ConDarth/MidiEVS/Documentation/EVIPCBLayout/EVIValvePCB.dxf

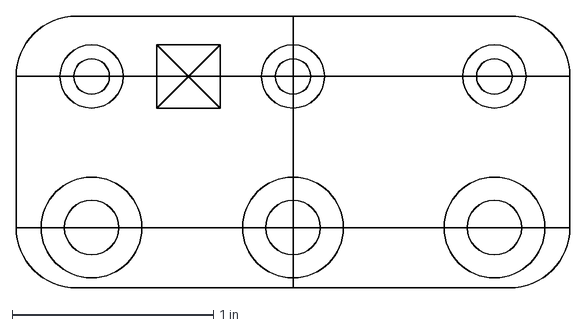
[picture p17: CAD file, 2022-07-06]
Documentation/EVIPCBLayout/EVIValvePCB.dxf
2.75 x 1.35 in
