ConDarth/MidiEVS/EVImk1/3d Files/MouthpieceFront.obj

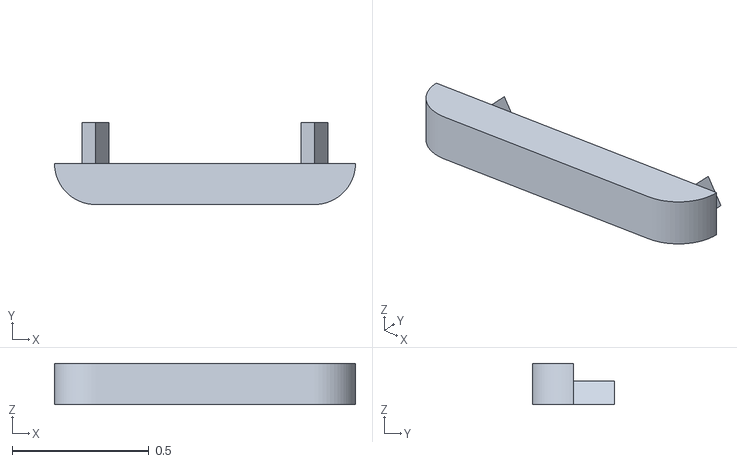
[picture p18: CAD file, 2019-05-07]
EVImk1/3d Files/MouthpieceFront.obj
1.10 x 0.3 x 0.15
