ConDarth/MidiEVS/EVImk3/EVImk3Cannister3.stl

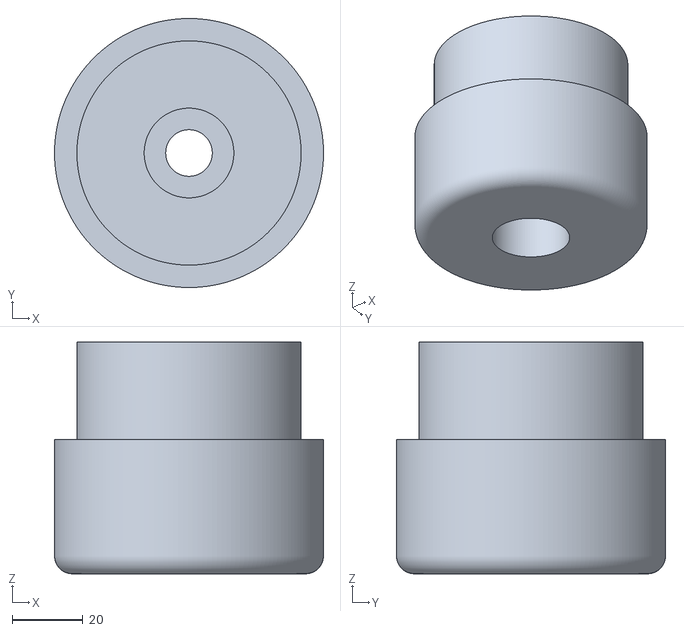
[picture p19: CAD file, 2022-07-06]
EVImk3/EVImk3Cannister3.stl
76.2 x 76.2 x 65.6
