ConDarth/MidiEVS/EVImk4/2D Files/EVImk4LidBottom.dxf

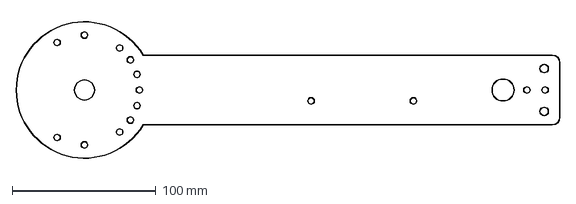
[picture p20: CAD file, 2023-05-10]
EVImk4/2D Files/EVImk4LidBottom.dxf
377.6 x 102.7 mm
