ConDarth/MidiEVS/EVImk4/3D Files/EVImk4Cannister2.stl

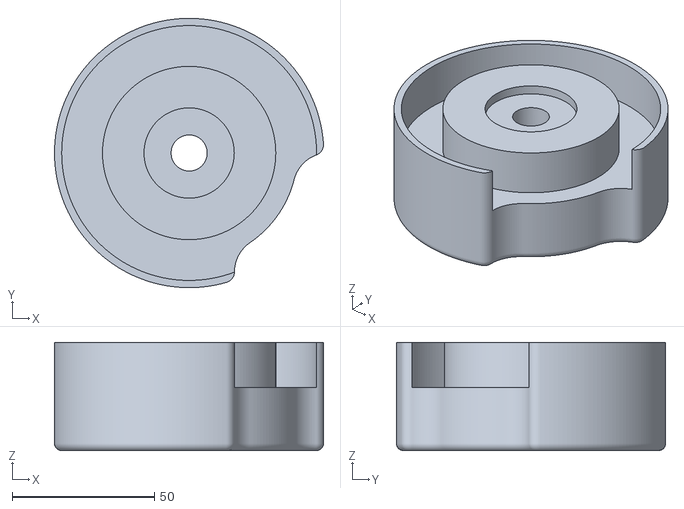
[picture p21: CAD file, 2023-05-10]
EVImk4/3D Files/EVImk4Cannister2.stl
94.6 x 94.7 x 38.1
