ConDarth/MidiEVS/Documentation/EVI3dCAD/Body3.2.stl

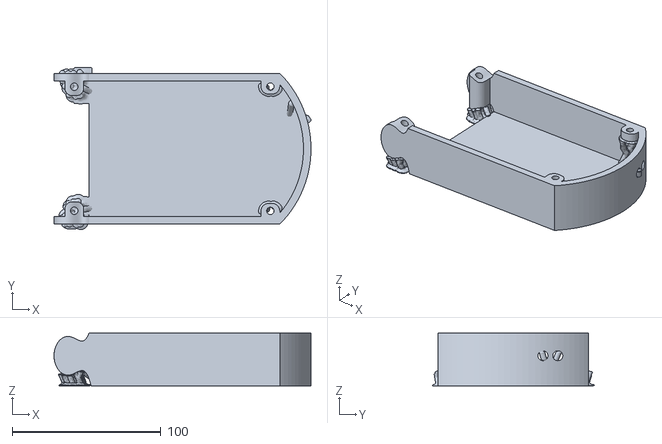
[picture p22: CAD file, 2021-01-06]
Documentation/EVI3dCAD/Body3.2.stl
173.0 x 109.2 x 35.7
