ConDarth/MidiEVS/EVImk1/3d Files/BasicCannsiter.obj

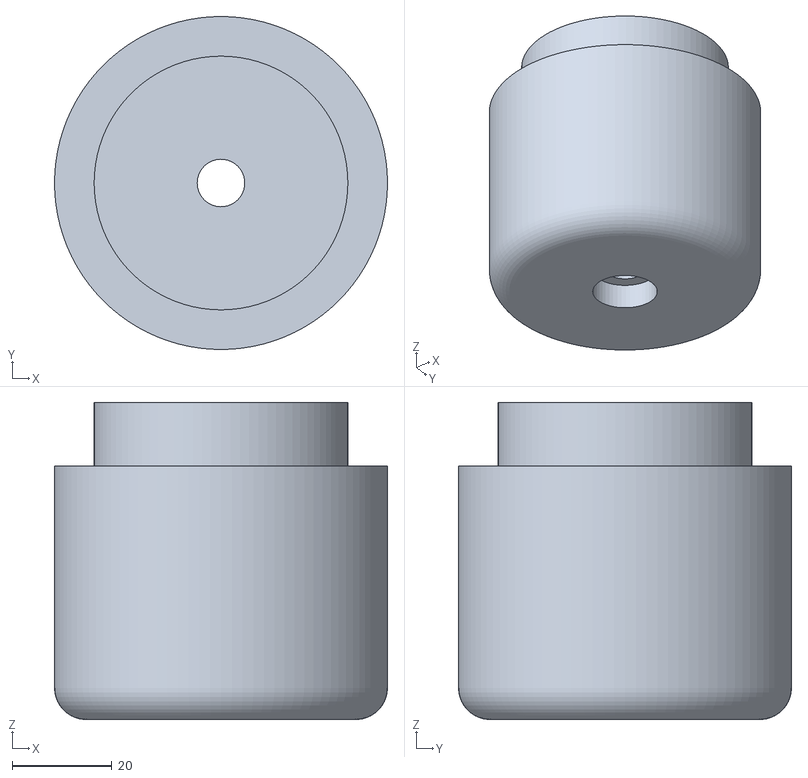
[picture p23: CAD file, 2019-05-07]
EVImk1/3d Files/BasicCannsiter.obj
66.7 x 66.7 x 63.5
