ConDarth/MidiEVS/EVImk3/EVImk3Mouthpeice.stl

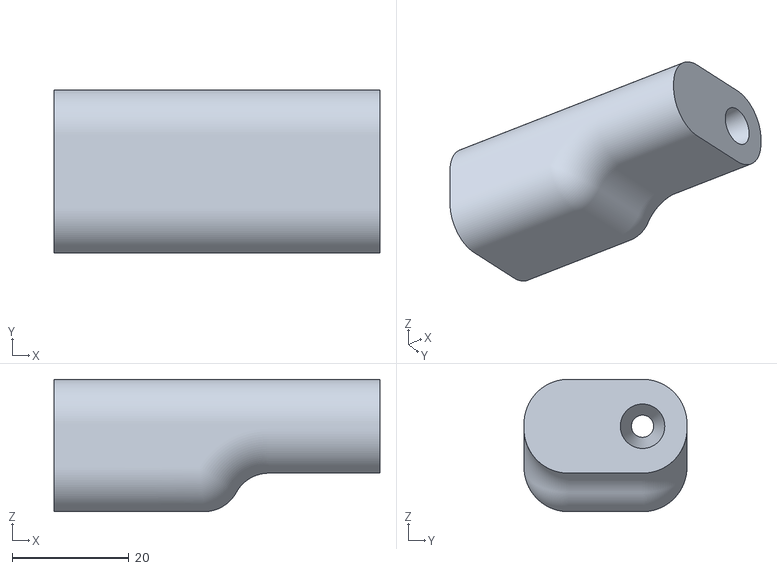
[picture p24: CAD file, 2022-07-06]
EVImk3/EVImk3Mouthpeice.stl
55.9 x 27.9 x 22.7
