ConDarth/MidiEVS/EVImk4/2D Files/EVImk4LidTop.dxf

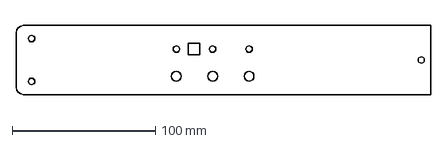
[picture p25: CAD file, 2023-05-10]
EVImk4/2D Files/EVImk4LidTop.dxf
289.4 x 48.3 mm
