ConDarth/MidiEVS/EVImk4/3D Files/EVImk4BodyFront4.stl

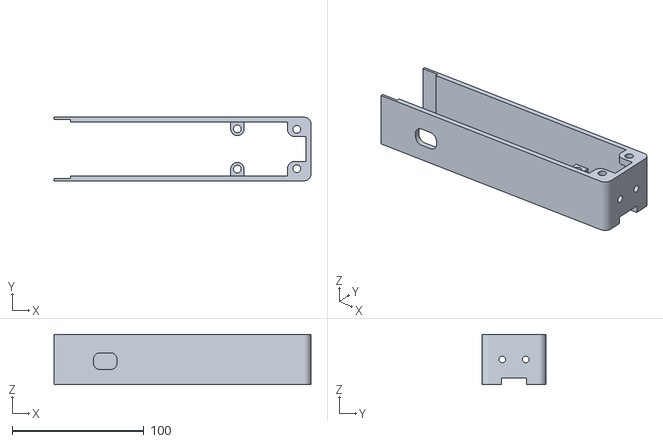
[picture p26: CAD file, 2023-05-10]
EVImk4/3D Files/EVImk4BodyFront4.stl
195.0 x 48.3 x 38.1
