ConDarth/MidiEVS/Documentation/EVI3dCAD/Mouthpeice1.0.stl

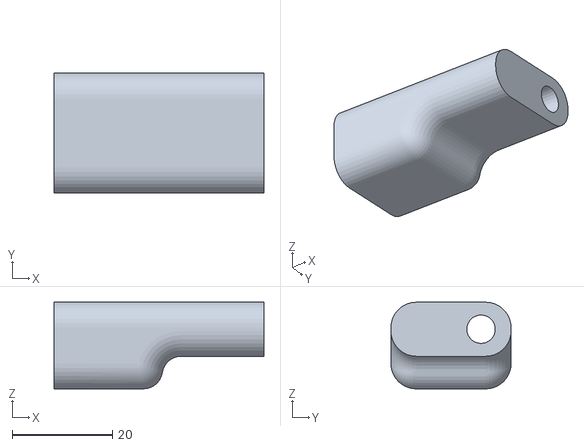
[picture p27: CAD file, 2021-01-06]
Documentation/EVI3dCAD/Mouthpeice1.0.stl
41.9 x 24.0 x 17.3
