ConDarth/MidiEVS/EVImk1/3d Files/MouthpieceTop.obj

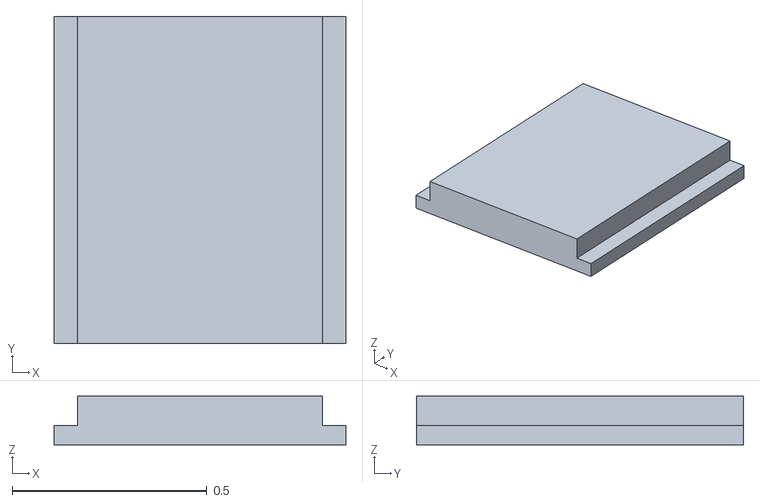
[picture p28: CAD file, 2019-05-07]
EVImk1/3d Files/MouthpieceTop.obj
0.75 x 0.84 x 0.125
