ConDarth/MidiEVS/EVImk3/EVImk3Cannister.stl

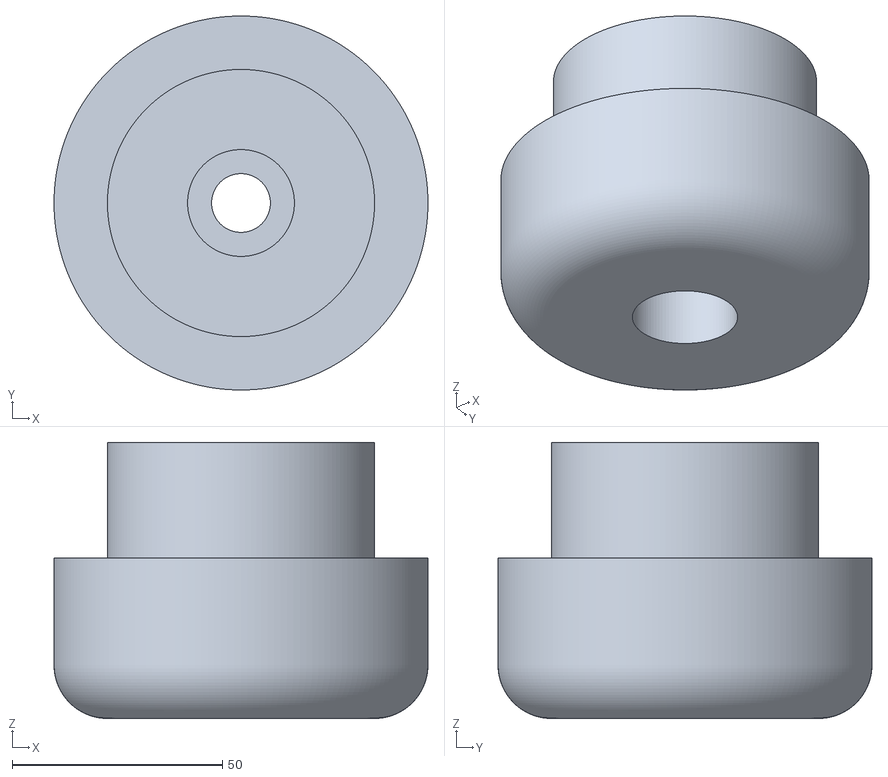
[picture p29: CAD file, 2022-07-06]
EVImk3/EVImk3Cannister.stl
88.9 x 88.9 x 65.6
