ConDarth/MidiEVS/EVImk4/3D Files/EVImk4LidTop.stl

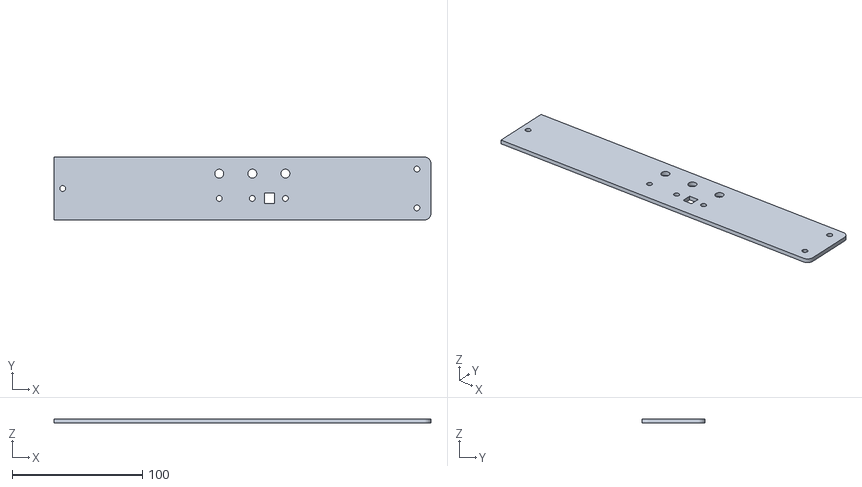
[picture p30: CAD file, 2023-05-10]
EVImk4/3D Files/EVImk4LidTop.stl
289.4 x 48.3 x 3.18
