ConDarth/MidiEVS/Documentation/EVI3dCAD/Body4.1.stl

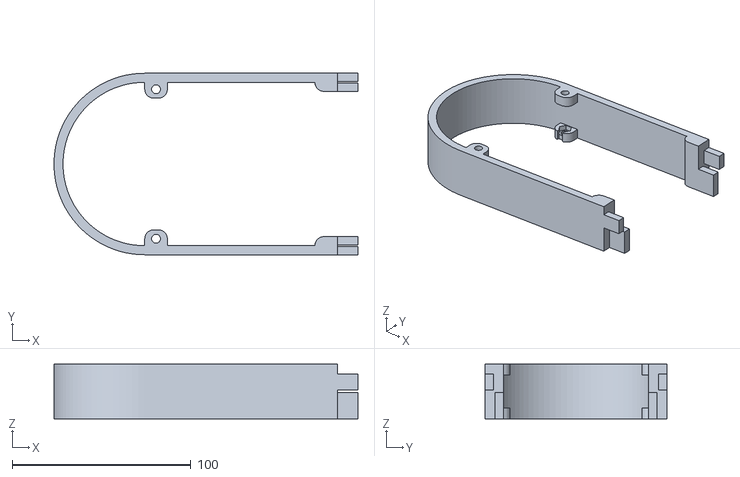
[picture p31: CAD file, 2021-01-06]
Documentation/EVI3dCAD/Body4.1.stl
170.1 x 101.6 x 30.6
