ConDarth/MidiEVS/EVImk3/EVImk3BackPlate.stl

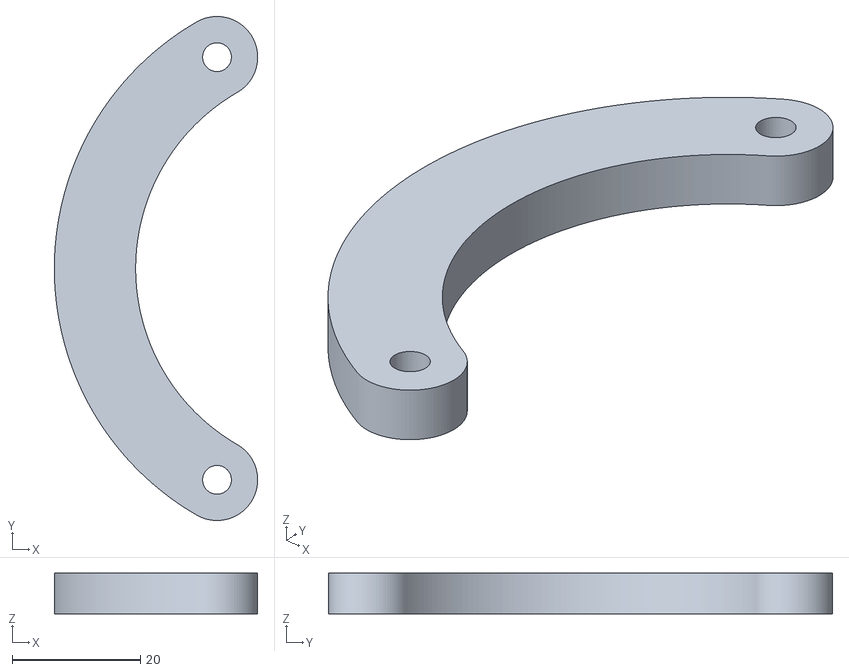
[picture p32: CAD file, 2022-07-06]
EVImk3/EVImk3BackPlate.stl
31.7 x 78.7 x 6.35
