ConDarth/MidiEVS/Documentation/EVI3dCAD/Body2.2.stl

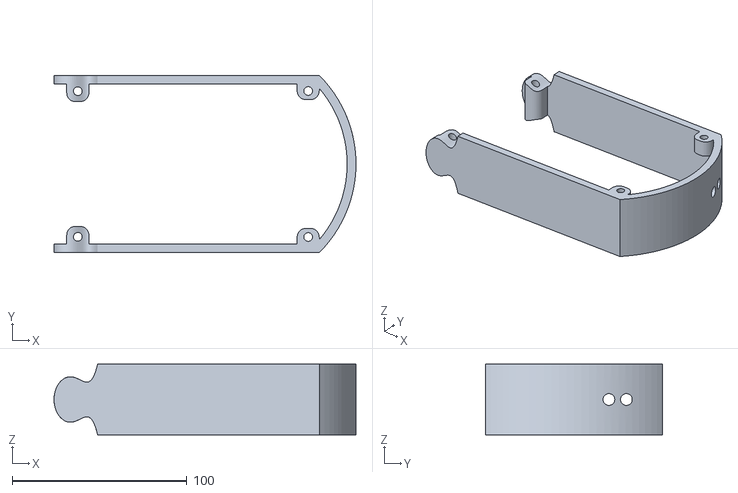
[picture p33: CAD file, 2021-01-06]
Documentation/EVI3dCAD/Body2.2.stl
173.0 x 101.6 x 40.6
