ConDarth/MidiEVS/EVImk4/3D Files/EVImk4PBPlate3.stl

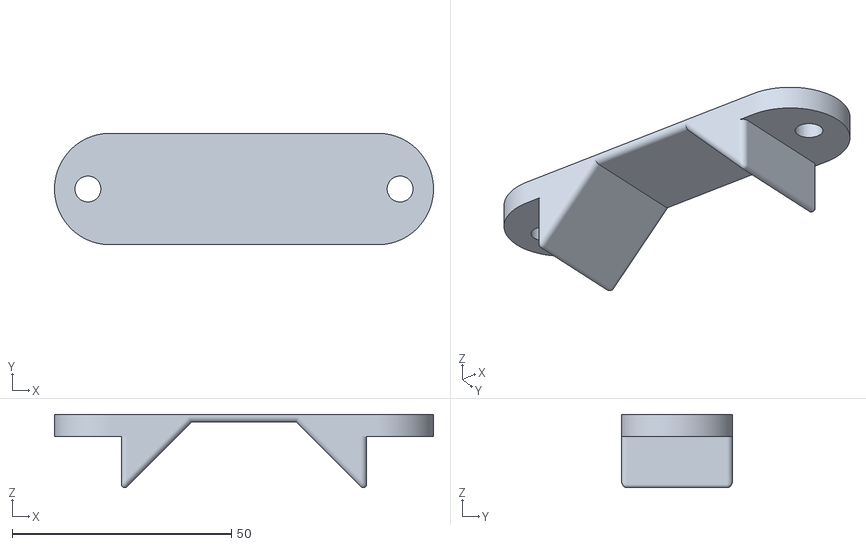
[picture p35: CAD file, 2023-05-10]
EVImk4/3D Files/EVImk4PBPlate3.stl
86.4 x 25.4 x 16.7
