ConDarth/MidiEVS/Documentation/EVI3dCAD/WarpTester1.0.stl

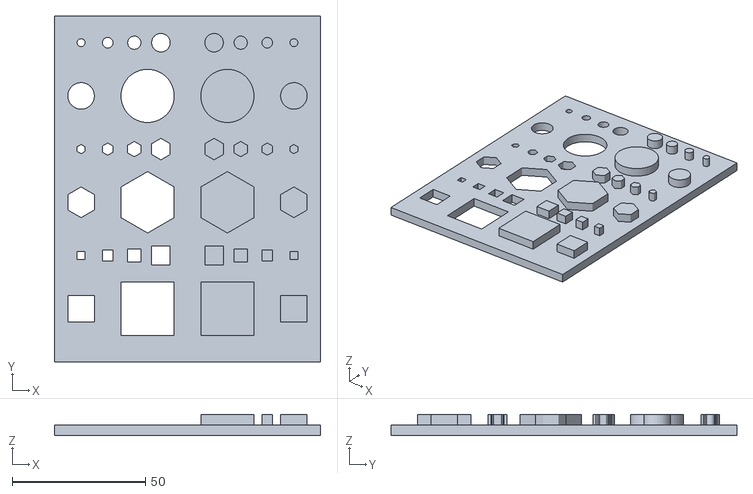
[picture p36: CAD file, 2021-01-06]
Documentation/EVI3dCAD/WarpTester1.0.stl
100.0 x 130.0 x 8.00
