ConDarth/MidiEVS/EVImk4/3D Files/EVImk4BodyBack4.stl

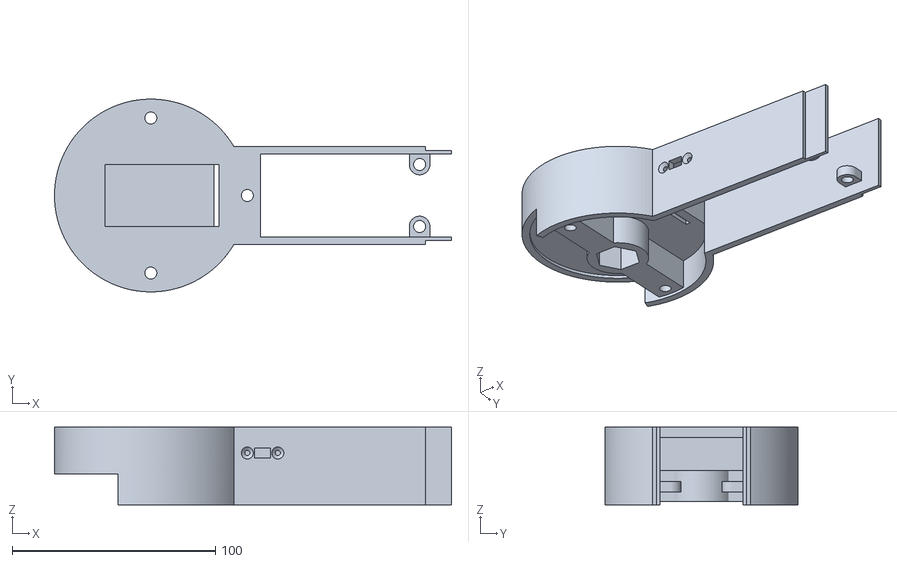
[picture p37: CAD file, 2023-05-10]
EVImk4/3D Files/EVImk4BodyBack4.stl
195.1 x 94.7 x 38.1
