ConDarth/MidiEVS/Documentation/EVI3dCAD/Body4.5.stl

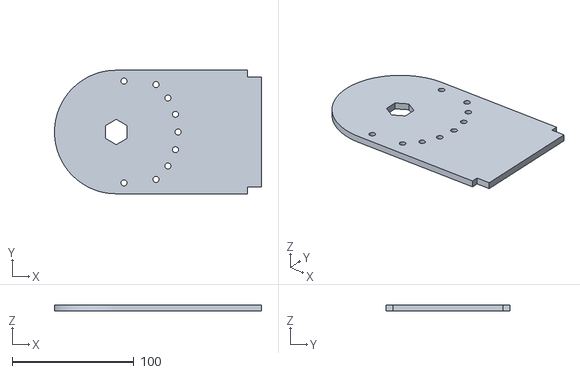
[picture p38: CAD file, 2021-01-06]
Documentation/EVI3dCAD/Body4.5.stl
170.1 x 101.6 x 5.08
