ConDarth/MidiEVS/EVImk3/EVImk3PBPad3.stl

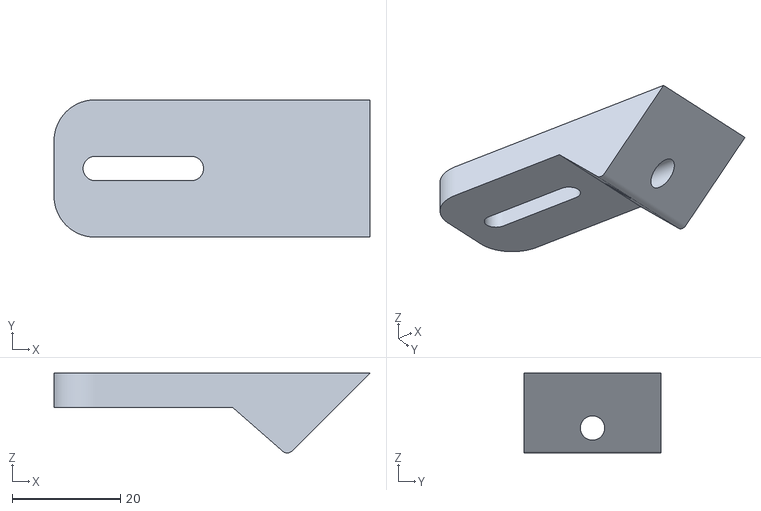
[picture p39: CAD file, 2022-07-06]
EVImk3/EVImk3PBPad3.stl
58.4 x 25.4 x 14.8
