ConDarth/MidiEVS/Documentation/EVI3dCAD/Body3.4.stl

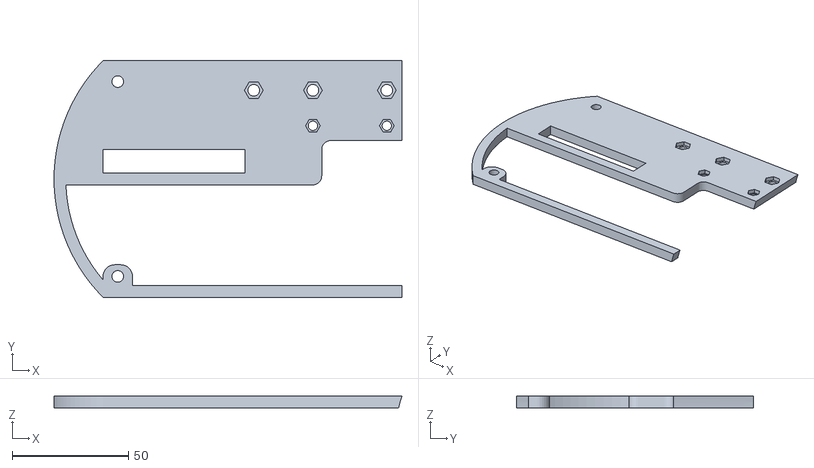
[picture p40: CAD file, 2021-01-06]
Documentation/EVI3dCAD/Body3.4.stl
149.5 x 101.6 x 5.00
