ConDarth/MidiEVS/EVImk3/EVImk3PBPad.stl

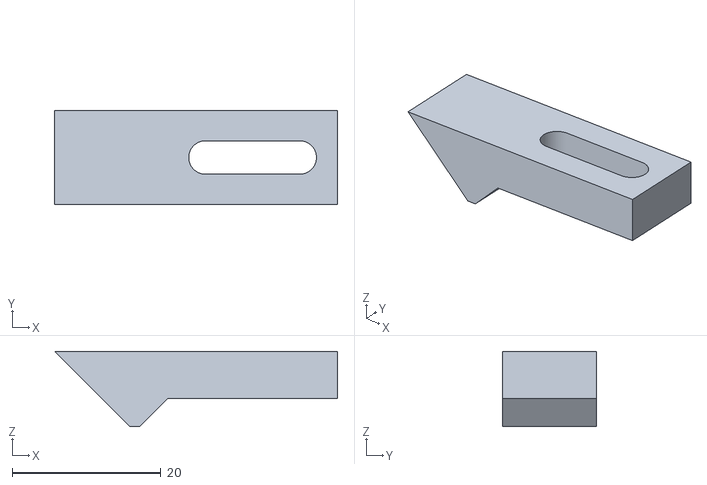
[picture p41: CAD file, 2022-07-06]
EVImk3/EVImk3PBPad.stl
38.1 x 12.7 x 10.2
