ConDarth/MidiEVS/EVImk3/EVImk3Cannister2.stl

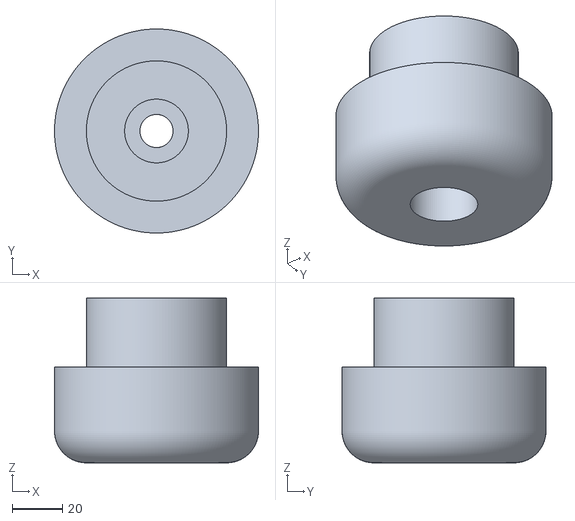
[picture p42: CAD file, 2022-07-06]
EVImk3/EVImk3Cannister2.stl
81.3 x 81.3 x 65.6
