ConDarth/MidiEVS/EVImk4/3D Files/EVImk4Cannister.stl

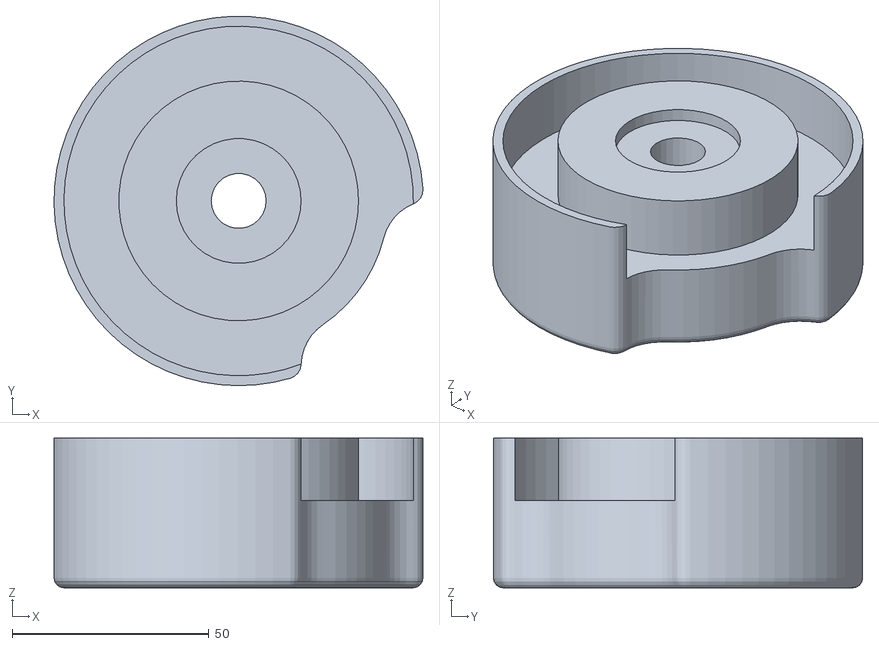
[picture p43: CAD file, 2022-07-06]
EVImk4/3D Files/EVImk4Cannister.stl
93.9 x 93.9 x 38.1
