ConDarth/MidiEVS/Documentation/EVI3dCAD/Body2.1.stl

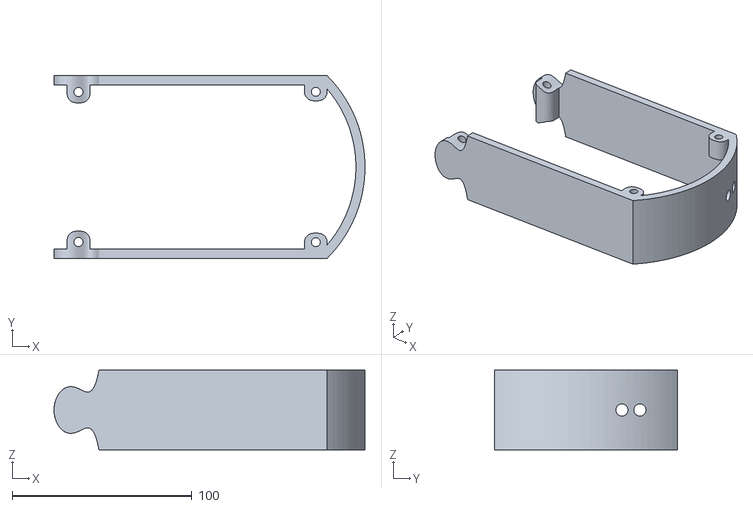
[picture p44: CAD file, 2021-01-06]
Documentation/EVI3dCAD/Body2.1.stl
173.0 x 101.6 x 44.5
