ConDarth/MidiEVS/EVImk3/EVImk3Neck.stl

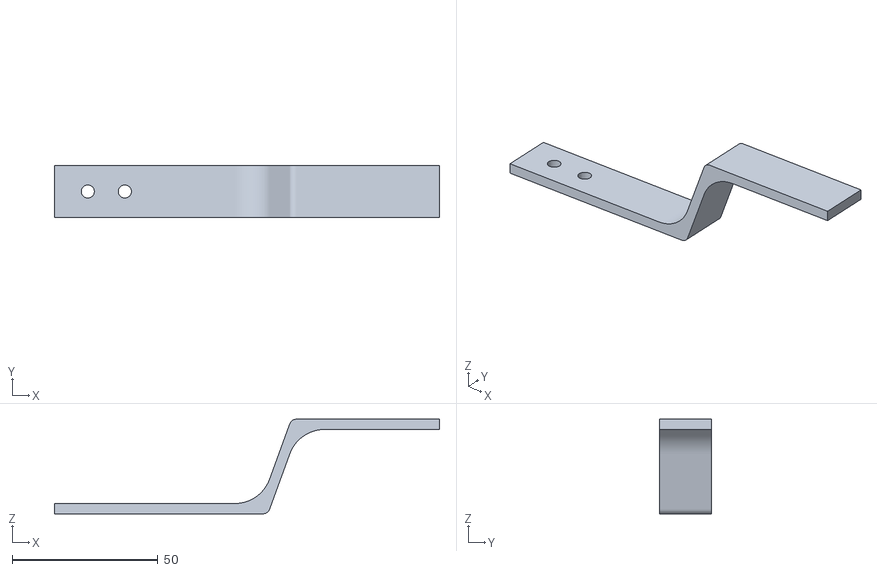
[picture p45: CAD file, 2022-07-06]
EVImk3/EVImk3Neck.stl
132.1 x 17.8 x 32.5
