ConDarth/MidiEVS/EVImk4/3D Files/EVImk4Mouthpeice2.stl

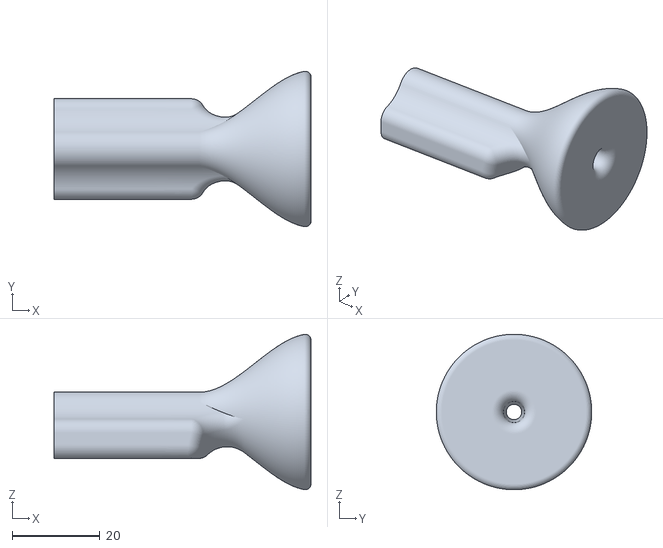
[picture p46: CAD file, 2022-07-06]
EVImk4/3D Files/EVImk4Mouthpeice2.stl
58.4 x 35.3 x 35.3
