ConDarth/MidiEVS/Documentation/EVI3dCAD/Cannister1.1.stl

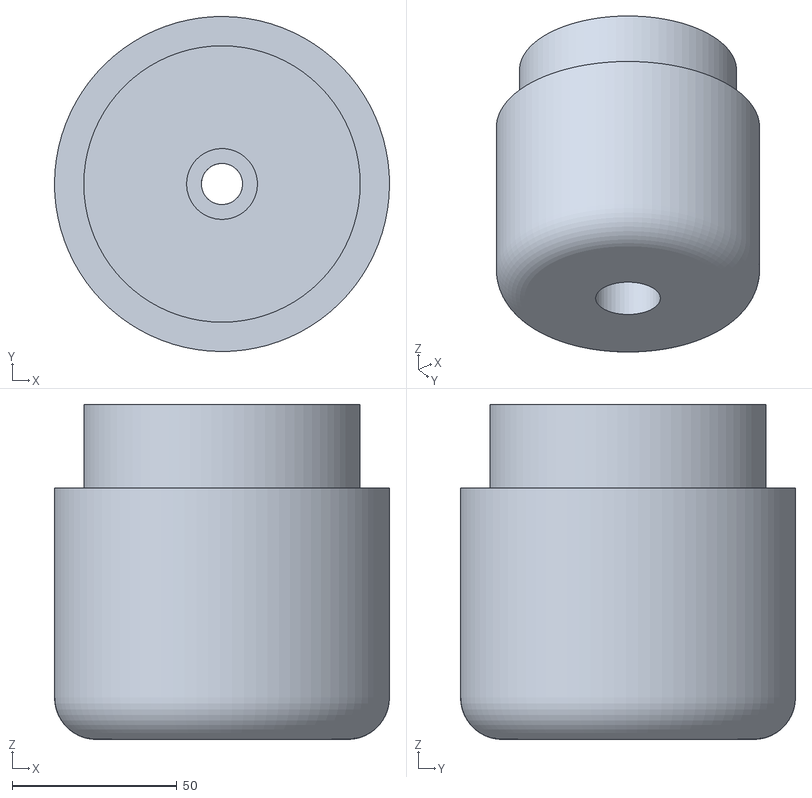
[picture p47: CAD file, 2021-01-06]
Documentation/EVI3dCAD/Cannister1.1.stl
101.6 x 101.6 x 101.6
