ConDarth/MidiEVS/EVImk4/3D Files/EVImk4Neck.stl

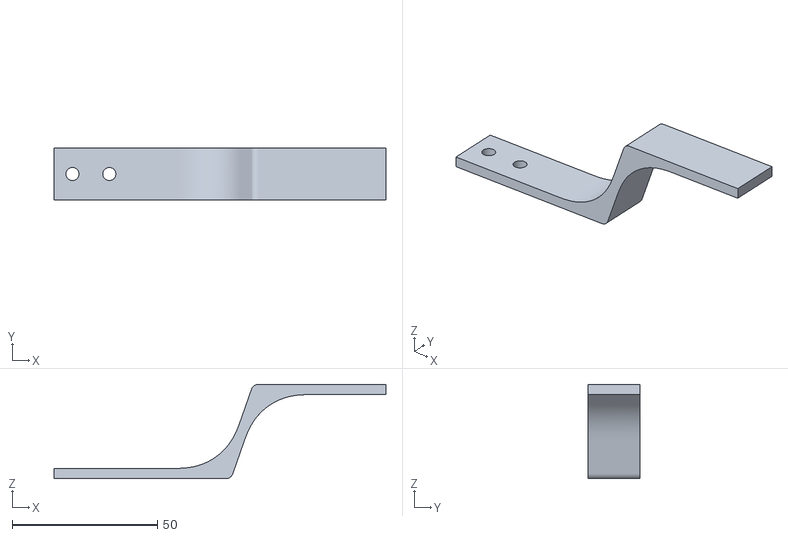
[picture p48: CAD file, 2022-07-06]
EVImk4/3D Files/EVImk4Neck.stl
114.3 x 17.8 x 32.5
