ConDarth/MidiEVS/Documentation/EVI3dCAD/Body3.3.stl

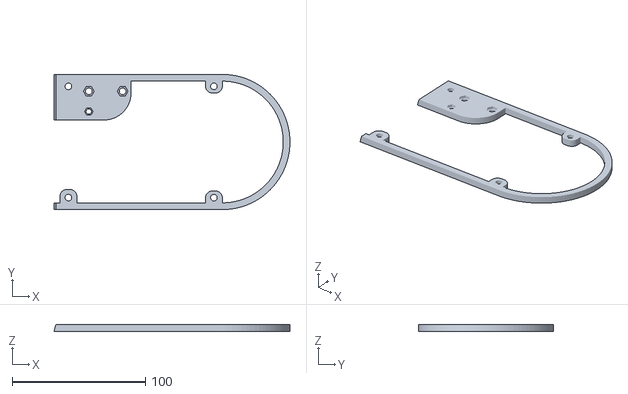
[picture p49: CAD file, 2021-01-06]
Documentation/EVI3dCAD/Body3.3.stl
177.3 x 101.6 x 5.00
