ConDarth/MidiEVS/EVImk4/3D Files/EVImk4PartialPad2.stl

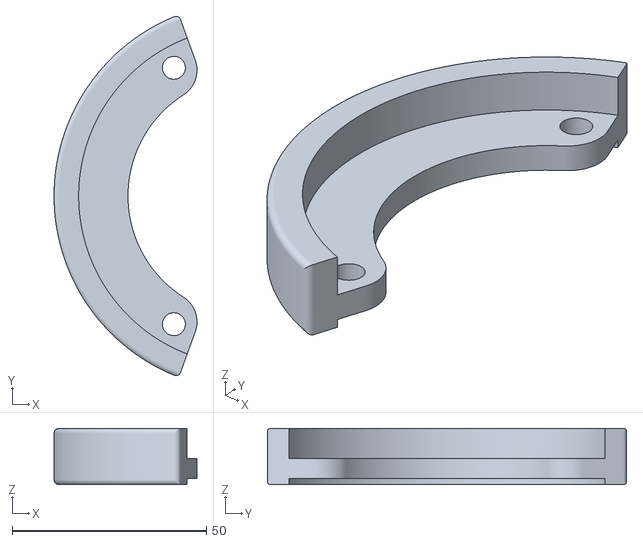
[picture p50: CAD file, 2022-07-06]
EVImk4/3D Files/EVImk4PartialPad2.stl
36.8 x 92.5 x 14.5
