ConDarth/MidiEVS/Documentation/EVI3dCAD/Body1.1.stl

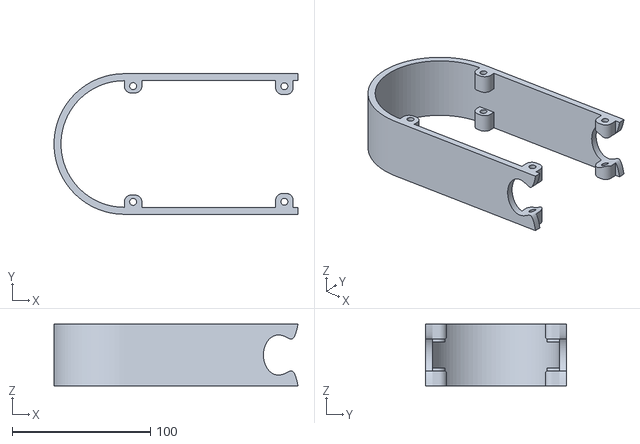
[picture p51: CAD file, 2021-01-06]
Documentation/EVI3dCAD/Body1.1.stl
176.3 x 101.6 x 44.5
