ConDarth/MidiEVS/EVImk4/3D Files/EVImk4Mouthpeice4.stl

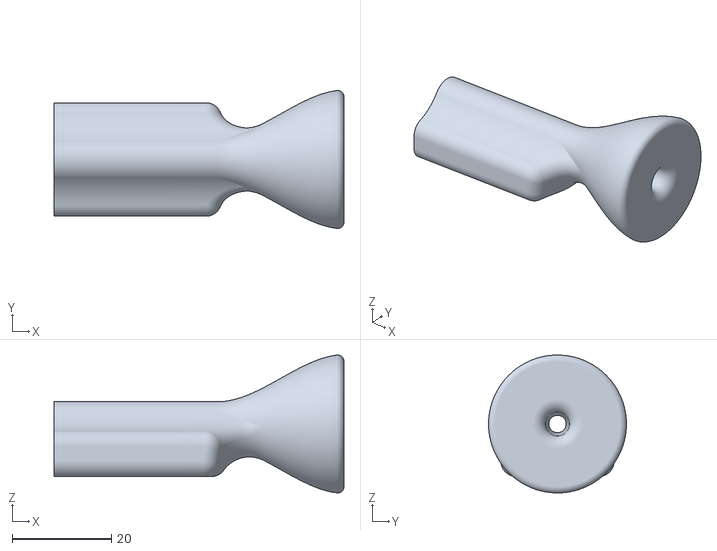
[picture p52: CAD file, 2022-07-06]
EVImk4/3D Files/EVImk4Mouthpeice4.stl
58.4 x 27.8 x 27.8
