ConDarth/MidiEVS/Documentation/EVI3dCAD/Body1.2.stl

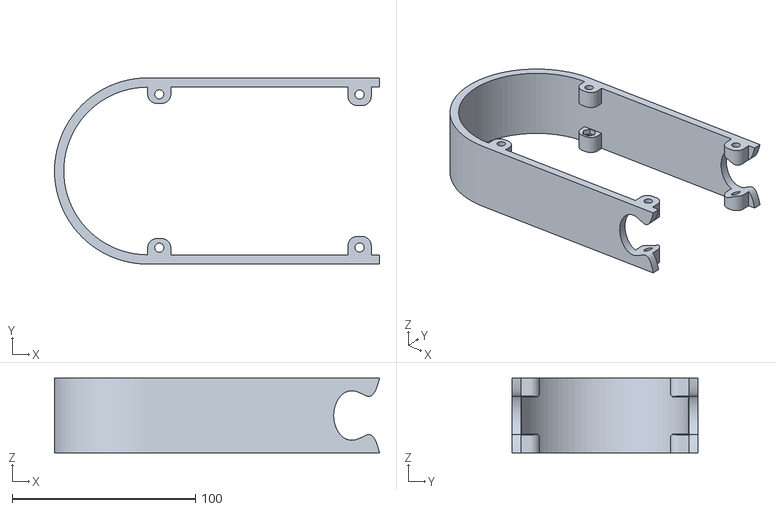
[picture p53: CAD file, 2021-01-06]
Documentation/EVI3dCAD/Body1.2.stl
177.3 x 101.6 x 40.6
