ConDarth/MidiEVS/EVImk4/3D Files/EVImk4BodyFront.stl

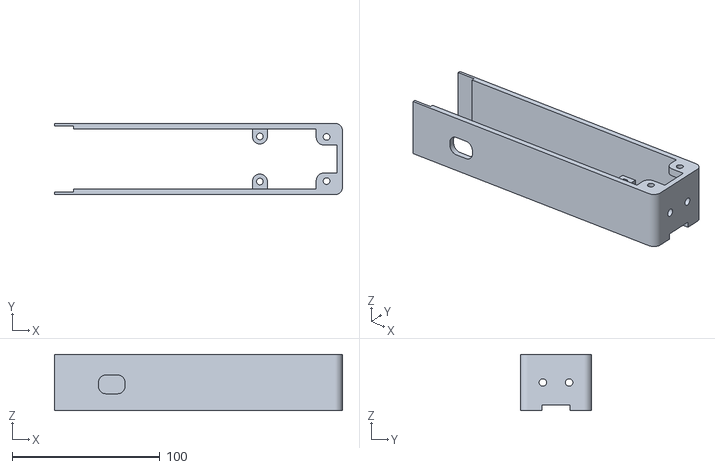
[picture p54: CAD file, 2022-07-06]
EVImk4/3D Files/EVImk4BodyFront.stl
194.8 x 48.3 x 38.1
