ConDarth/MidiEVS/Documentation/EVI3dCAD/Body3.1.stl

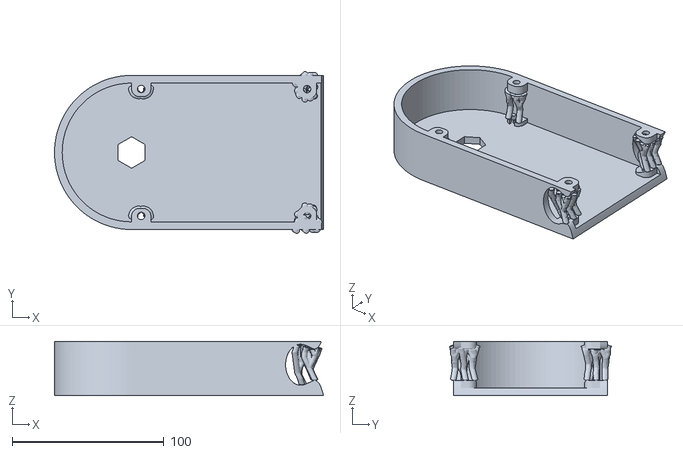
[picture p55: CAD file, 2021-01-06]
Documentation/EVI3dCAD/Body3.1.stl
177.3 x 106.6 x 35.6
