ConDarth/MidiEVS/EVImk4/3D Files/EVImk4BodyBack2.stl

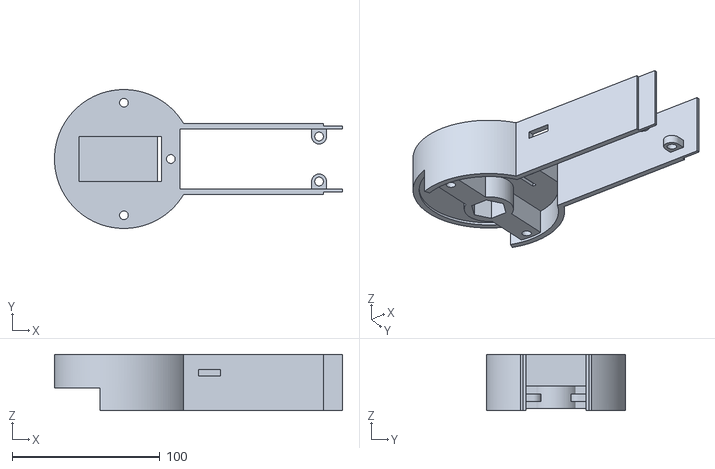
[picture p56: CAD file, 2022-07-06]
EVImk4/3D Files/EVImk4BodyBack2.stl
194.9 x 94.0 x 38.1
