ConDarth/MidiEVS/EVImk4/3D Files/EVImk4PBPlate2.stl

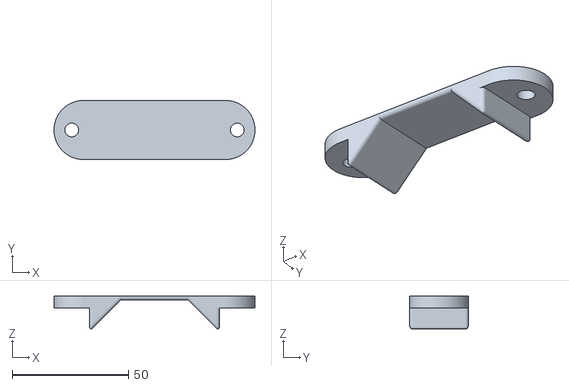
[picture p58: CAD file, 2022-07-06]
EVImk4/3D Files/EVImk4PBPlate2.stl
86.4 x 25.4 x 14.2
