ConDarth/MidiEVS/EVImk4/3D Files/ThreadedInsertTester.stl

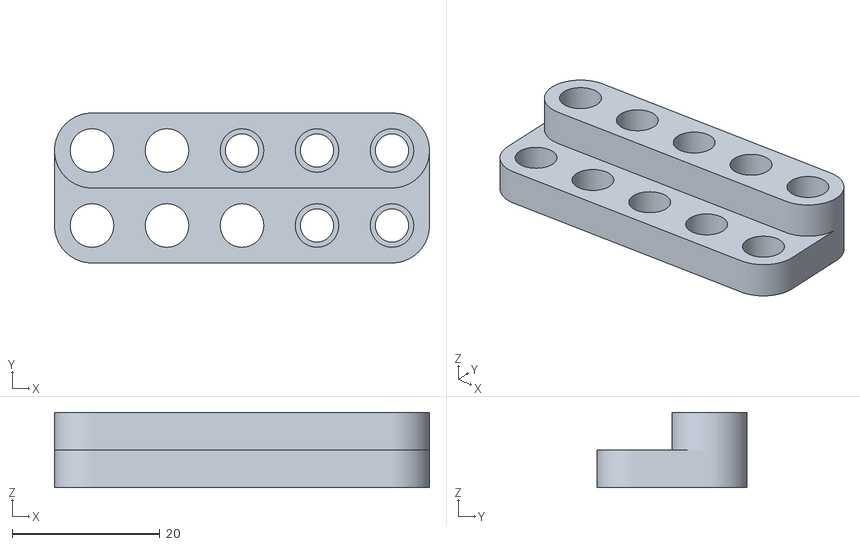
[picture p60: CAD file, 2022-07-06]
EVImk4/3D Files/ThreadedInsertTester.stl
50.8 x 20.3 x 10.2
