ConDarth/MidiEVS/EVImk4/3D Files/EVImk4Mouthpeice.stl

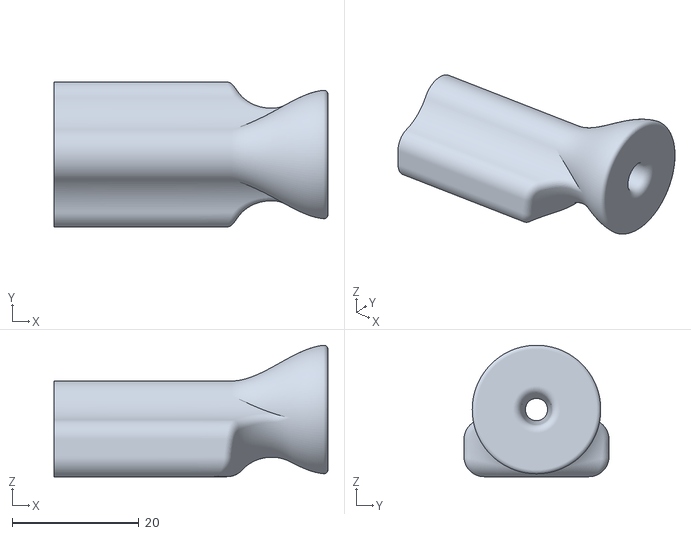
[picture p61: CAD file, 2022-07-06]
EVImk4/3D Files/EVImk4Mouthpeice.stl
43.2 x 22.9 x 20.7
