ConDarth/MidiEVS/EVImk4/3D Files/EVImk4PartialPad.stl

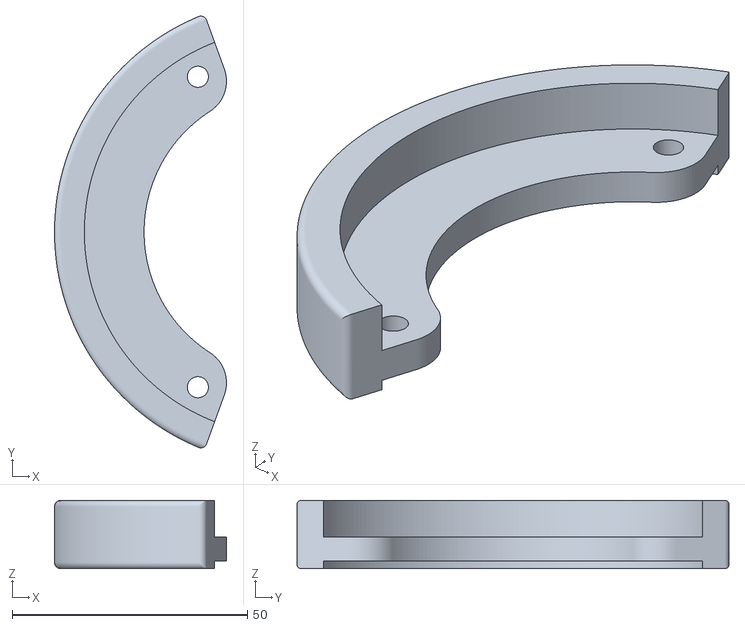
[picture p62: CAD file, 2022-07-06]
EVImk4/3D Files/EVImk4PartialPad.stl
36.6 x 91.8 x 14.5
