ConDarth/MidiEVS/EVImk1/Advanved Operation Tests/CapSenseTest/CapSenseTest.ino

#include <CapacitiveSensor.h>

/*
 * CapitiveSense Library Demo Sketch
 * Paul Badger 2008
 * Uses a high value resistor e.g. 10M between send pin and receive pin
 * Resistor effects sensitivity, experiment with values, 50K - 50M. Larger resistor values yield larger sensor values.
 * Receive pin is the sensor pin - try different amounts of foil/metal on this pin
 */


CapacitiveSensor   cs_4_2 = CapacitiveSensor(2,4);        // 10M resistor between pins 4 & 2, pin 2 is sensor pin, add a wire and or foil if desired


void setup()                    
{
   Serial.begin(9600);
}

void loop()                    
{
    long start = millis();
    long total1 =  cs_4_2.capacitiveSensor(30);
    

    Serial.print(millis() - start);        // check on performance in milliseconds
    Serial.print("\t");                    // tab character for debug windown spacing

    Serial.println(total1);                  // print sensor output 1
    

                                // arbitrary delay to limit data to serial port 
}
